apdlv72/VitoWifi/favicon.ico.h

//unsigned char resources_favicon_ico[] = 
{
  0x00, 0x00, 0x01, 0x00, 0x01, 0x00, 0x10, 0x10, 0x00, 0x00, 0x01, 0x00,
  0x08, 0x00, 0x68, 0x05, 0x00, 0x00, 0x16, 0x00, 0x00, 0x00, 0x28, 0x00,
  0x00, 0x00, 0x10, 0x00, 0x00, 0x00, 0x20, 0x00, 0x00, 0x00, 0x01, 0x00,
  0x08, 0x00, 0x00, 0x00, 0x00, 0x00, 0x00, 0x01, 0x00, 0x00, 0x00, 0x00,
  0x00, 0x00, 0x00, 0x00, 0x00, 0x00, 0x00, 0x01, 0x00, 0x00, 0x00, 0x00,
  0x00, 0x00, 0xe6, 0xb7, 0x48, 0x00, 0xe2, 0xd1, 0x8c, 0x00, 0xf8, 0xf9,
  0xf0, 0x00, 0xef, 0xcf, 0x86, 0x00, 0xcf, 0x99, 0x02, 0x00, 0xdb, 0xac,
  0x31, 0x00, 0xcb, 0x97, 0x17, 0x00, 0xd9, 0x96, 0x02, 0x00, 0xfd, 0xfc,
  0xf9, 0x00, 0xd9, 0x99, 0x02, 0x00, 0xdd, 0xc8, 0x72, 0x00, 0xfc, 0xfe,
  0xff, 0x00, 0xff, 0xfd, 0xfc, 0x00, 0xe5, 0xc4, 0x6f, 0x00, 0xe3, 0x9c,
  0x02, 0x00, 0xf6, 0xf8, 0xe5, 0x00, 0xf6, 0xe1, 0xb3, 0x00, 0xfb, 0xf9,
  0xfa, 0x00, 0xfd, 0xfe, 0xf7, 0x00, 0xd6, 0x9a, 0x06, 0x00, 0xdc, 0x95,
  0x00, 0x00, 0xfd, 0xff, 0xfa, 0x00, 0xff, 0xfe, 0xf7, 0x00, 0xfe, 0xff,
  0xfa, 0x00, 0xd9, 0x9c, 0x03, 0x00, 0xfe, 0xfd, 0xfd, 0x00, 0xff, 0xff,
  0xfa, 0x00, 0xdc, 0x9c, 0x03, 0x00, 0xdd, 0x9c, 0x03, 0x00, 0xe2, 0x99,
  0x03, 0x00, 0xe0, 0x9c, 0x03, 0x00, 0xe0, 0xa1, 0x09, 0x00, 0xe2, 0xb8,
  0x44, 0x00, 0xed, 0xe2, 0xb7, 0x00, 0xe4, 0x9c, 0x1e, 0x00, 0xfc, 0xf8,
  0xe6, 0x00, 0xd9, 0xa9, 0x33, 0x00, 0xf7, 0xf9, 0xfb, 0x00, 0xd1, 0x99,
  0x04, 0x00, 0xf6, 0xfd, 0xfe, 0x00, 0xfc, 0xf9, 0xfb, 0x00, 0xd9, 0x98,
  0x01, 0x00, 0xdd, 0xac, 0x3c, 0x00, 0xfc, 0xfd, 0xfe, 0x00, 0xda, 0x9b,
  0x01, 0x00, 0xfd, 0xff, 0xfb, 0x00, 0xd9, 0x9e, 0x01, 0x00, 0xea, 0xa9,
  0x2a, 0x00, 0xda, 0x9c, 0x04, 0x00, 0xdc, 0x9e, 0x01, 0x00, 0xe8, 0xc4,
  0x71, 0x00, 0xe1, 0x99, 0x04, 0x00, 0xdd, 0xa4, 0x01, 0x00, 0xe3, 0x99,
  0x04, 0x00, 0xde, 0x9c, 0x0d, 0x00, 0xf8, 0xe9, 0xde, 0x00, 0xe5, 0x97,
  0x07, 0x00, 0xdc, 0xb9, 0x51, 0x00, 0xe4, 0x9b, 0x13, 0x00, 0xfa, 0xe4,
  0xac, 0x00, 0xd2, 0x94, 0x11, 0x00, 0xd1, 0x9f, 0x05, 0x00, 0xfc, 0xfb,
  0xf9, 0x00, 0xfd, 0xff, 0xf3, 0x00, 0xd8, 0x96, 0x05, 0x00, 0xfb, 0xfa,
  0xff, 0x00, 0xd7, 0x9b, 0x02, 0x00, 0xd5, 0x9e, 0x02, 0x00, 0xfe, 0xfb,
  0xf9, 0x00, 0xd8, 0x9b, 0x02, 0x00, 0xfc, 0xff, 0xfc, 0x00, 0xe1, 0xad,
  0x37, 0x00, 0xfe, 0xfd, 0xff, 0x00, 0xfe, 0xff, 0xfc, 0x00, 0xff, 0xff,
  0xfc, 0x00, 0xdc, 0x97, 0x08, 0x00, 0xe2, 0x95, 0x02, 0x00, 0xdb, 0x9f,
  0x05, 0x00, 0xde, 0x9e, 0x02, 0x00, 0xe2, 0x9b, 0x02, 0x00, 0xe0, 0x9c,
  0x05, 0x00, 0xf2, 0xda, 0xa1, 0x00, 0xe4, 0x9b, 0x02, 0x00, 0xdf, 0x9c,
  0x0e, 0x00, 0xed, 0xd3, 0x7b, 0x00, 0xd3, 0x8f, 0x03, 0x00, 0xf9, 0xdc,
  0xb9, 0x00, 0xf8, 0xfb, 0xf1, 0x00, 0xf4, 0xe6, 0xbc, 0x00, 0xf8, 0xf6,
  0xfd, 0x00, 0xe9, 0xd4, 0x99, 0x00, 0xda, 0x95, 0x03, 0x00, 0xd8, 0x9a,
  0x00, 0x00, 0xf9, 0xff, 0xfd, 0x00, 0xfe, 0xfd, 0xf7, 0x00, 0xd9, 0x9a,
  0x00, 0x00, 0xdc, 0x95, 0x03, 0x00, 0xf8, 0xeb, 0xc2, 0x00, 0xfe, 0xfc,
  0xfd, 0x00, 0xff, 0xfe, 0xfa, 0x00, 0xff, 0xff, 0xfd, 0x00, 0xdc, 0x9c,
  0x06, 0x00, 0xe0, 0x9b, 0x03, 0x00, 0xe4, 0x96, 0x06, 0x00, 0xdb, 0xa1,
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
};
//unsigned int resources_favicon_ico_len = 1406;
