apdlv72/VitoWifi/fan.png.h

//unsigned char fan_small_png[] =
{
  0x89, 0x50, 0x4e, 0x47, 0x0d, 0x0a, 0x1a, 0x0a, 0x00, 0x00, 0x00, 0x0d,
  0x49, 0x48, 0x44, 0x52, 0x00, 0x00, 0x00, 0x48, 0x00, 0x00, 0x00, 0x48,
  0x08, 0x03, 0x00, 0x00, 0x00, 0x62, 0x33, 0x43, 0x75, 0x00, 0x00, 0x00,
  0x33, 0x50, 0x4c, 0x54, 0x45, 0xc0, 0x96, 0x18, 0x00, 0x00, 0x8c, 0x00,
  0x00, 0xb6, 0x05, 0x00, 0xd1, 0x04, 0x0d, 0x82, 0x10, 0x00, 0xfa, 0x11,
  0x2c, 0x93, 0x2f, 0x4e, 0xa3, 0x49, 0x7b, 0xba, 0x5e, 0x99, 0xc6, 0x60,
  0xa8, 0xca, 0x69, 0xaf, 0xd1, 0x74, 0xb5, 0xd2, 0x79, 0xba, 0xd7, 0x7d,
  0xbd, 0xdb, 0x89, 0xc2, 0xda, 0x9b, 0xca, 0xdf, 0x00, 0x61, 0xac, 0xee,
  0x00, 0x00, 0x00, 0x01, 0x74, 0x52, 0x4e, 0x53, 0x00, 0x40, 0xe6, 0xd8,
  0x66, 0x00, 0x00, 0x02, 0x5b, 0x49, 0x44, 0x41, 0x54, 0x58, 0xc3, 0xbd,
  0xd8, 0xd9, 0x62, 0xab, 0x20, 0x10, 0x06, 0x60, 0x54, 0xe2, 0xc2, 0xb0,
  0xf8, 0xfe, 0x4f, 0x5b, 0x56, 0x05, 0x64, 0x13, 0x39, 0x67, 0x7a, 0x55,
  0x9b, 0x7c, 0x01, 0xc4, 0x7f, 0x48, 0x11, 0x0a, 0x8b, 0xd8, 0x42, 0xdf,
  0x8a, 0xdc, 0x05, 0x83, 0x18, 0x55, 0x63, 0x1c, 0x4a, 0xe1, 0xbb, 0x43,
  0x94, 0x23, 0x6b, 0x94, 0x33, 0x00, 0x52, 0x0a, 0x63, 0x8c, 0x8e, 0x80,
  0x18, 0xe7, 0xbc, 0xe5, 0xb5, 0xa5, 0xbf, 0xa9, 0xa9, 0x29, 0x87, 0xd7,
  0x90, 0x94, 0x15, 0x2f, 0x11, 0xe3, 0x42, 0x88, 0x36, 0x27, 0x94, 0x1e,
  0x03, 0x12, 0x29, 0x88, 0x64, 0xea, 0x2d, 0x44, 0x48, 0x5d, 0xfa, 0xaf,
  0x10, 0x21, 0x0d, 0x52, 0x0c, 0x49, 0xe6, 0x3c, 0xdb, 0x1d, 0x52, 0x1a,
  0xd1, 0x2b, 0x88, 0xa4, 0xf7, 0x91, 0x1a, 0xd1, 0x19, 0x41, 0xa4, 0x0f,
  0xe2, 0x83, 0x20, 0xfa, 0x80, 0x48, 0x37, 0x24, 0xca, 0x10, 0x98, 0xaa,
  0xae, 0x36, 0x8f, 0x16, 0x29, 0x61, 0x5c, 0x95, 0x87, 0x12, 0x8b, 0x14,
  0x20, 0xf4, 0x2e, 0x95, 0xa4, 0x9a, 0x42, 0x6d, 0x73, 0xf3, 0x18, 0x6a,
  0xc3, 0x4a, 0x97, 0xc1, 0x94, 0x94, 0xcd, 0x91, 0x04, 0x64, 0x15, 0x9d,
  0x30, 0x42, 0xfe, 0xc8, 0x32, 0x94, 0x84, 0xca, 0x8f, 0xed, 0x2d, 0x5d,
  0xf9, 0xab, 0x14, 0x71, 0x97, 0xa4, 0x8c, 0x54, 0xc8, 0x48, 0xff, 0x69,
  0xbb, 0xe2, 0xd7, 0x2a, 0x72, 0xf9, 0x02, 0x09, 0x50, 0x63, 0x24, 0xd9,
  0xc5, 0x31, 0x97, 0x4e, 0x5b, 0x59, 0x28, 0x1e, 0x92, 0x17, 0x92, 0x36,
  0x34, 0xb9, 0xc7, 0x58, 0x49, 0x43, 0xa5, 0x20, 0x55, 0x33, 0xe1, 0x4e,
  0x8a, 0x9d, 0xe0, 0x3d, 0xb4, 0xd2, 0x1f, 0xc0, 0x2e, 0xac, 0xba, 0x7a,
  0x10, 0x7a, 0xcd, 0xeb, 0x75, 0x5b, 0x02, 0xb9, 0xd7, 0x18, 0x13, 0xfc,
  0x58, 0x31, 0x5e, 0xb7, 0x1d, 0x38, 0xcf, 0xb4, 0x83, 0x2a, 0xa5, 0x6f,
  0x37, 0xdb, 0xd7, 0x69, 0x9e, 0xe7, 0x09, 0x6f, 0x44, 0x70, 0xd1, 0xd9,
  0x2c, 0x95, 0x74, 0xe0, 0x79, 0xf9, 0xc9, 0x9a, 0xf1, 0xd6, 0xdf, 0xc0,
  0x25, 0x44, 0xb6, 0xe9, 0x67, 0x6a, 0xc6, 0x5f, 0x4e, 0x4b, 0x70, 0xac,
  0xb3, 0x85, 0x16, 0xfc, 0xe1, 0xe0, 0x85, 0xe0, 0xc0, 0x8b, 0x83, 0xa6,
  0x4f, 0x12, 0xc2, 0xd7, 0x88, 0xa6, 0xed, 0xd3, 0xc1, 0xf2, 0x82, 0x66,
  0xbc, 0x53, 0xf8, 0x70, 0x48, 0x5d, 0xa7, 0xc5, 0x0e, 0x68, 0x3d, 0x6c,
  0x82, 0xf5, 0x59, 0x87, 0xdc, 0x46, 0xcb, 0x6f, 0x91, 0x1b, 0x69, 0x67,
  0x3a, 0x77, 0xfa, 0xce, 0xce, 0x72, 0x2b, 0x1f, 0x1b, 0x9e, 0xa6, 0x09,
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
};
//unsigned int fan_small_png_len = 736;
